Darkone83/Theia/images/2D Back Transmitter.png

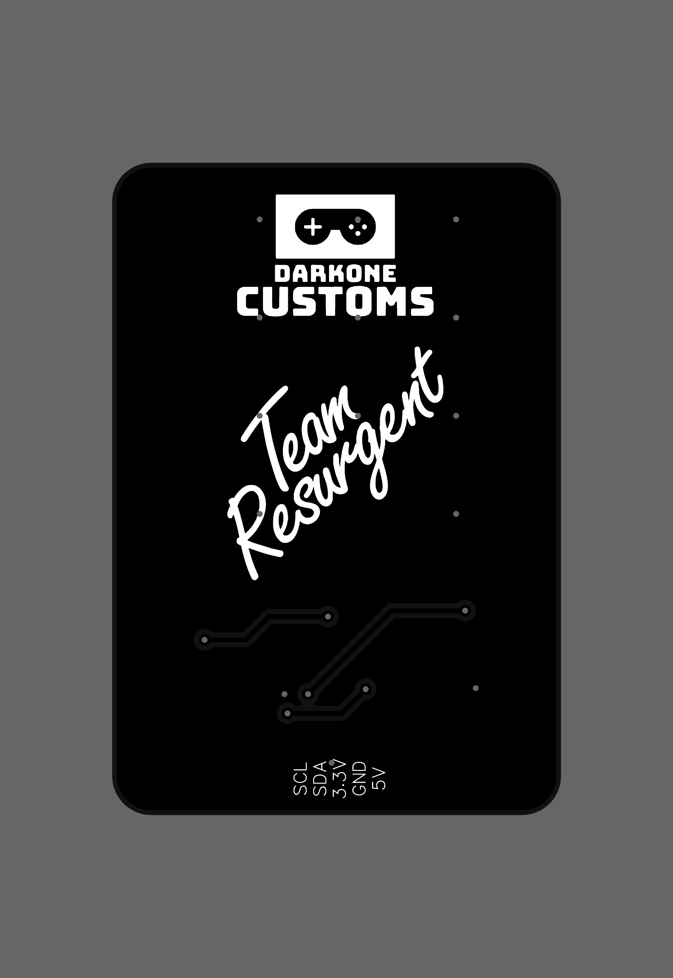
images/2D Back Transmitter.png
