Darkone83/Theia/images/3D Back Transmitter.png

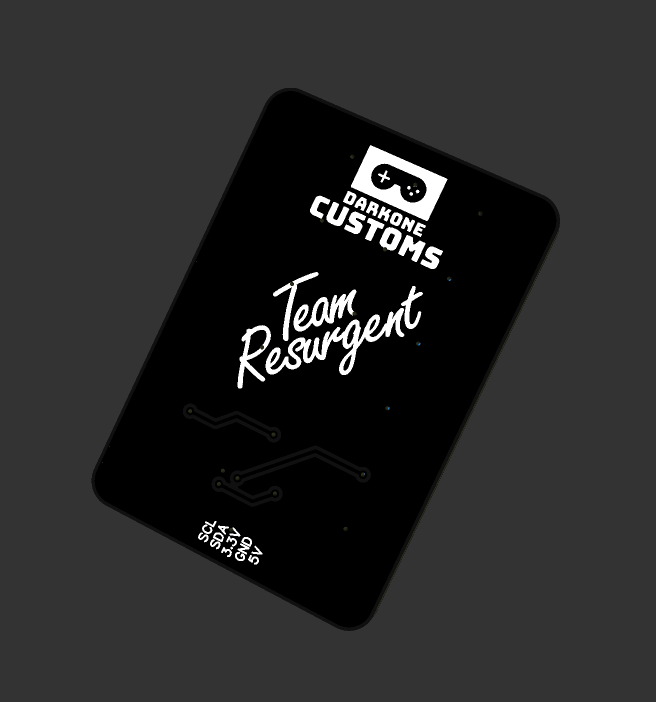
images/3D Back Transmitter.png
