Darkone83/Theia/images/3D Front US2066 Backpack.png

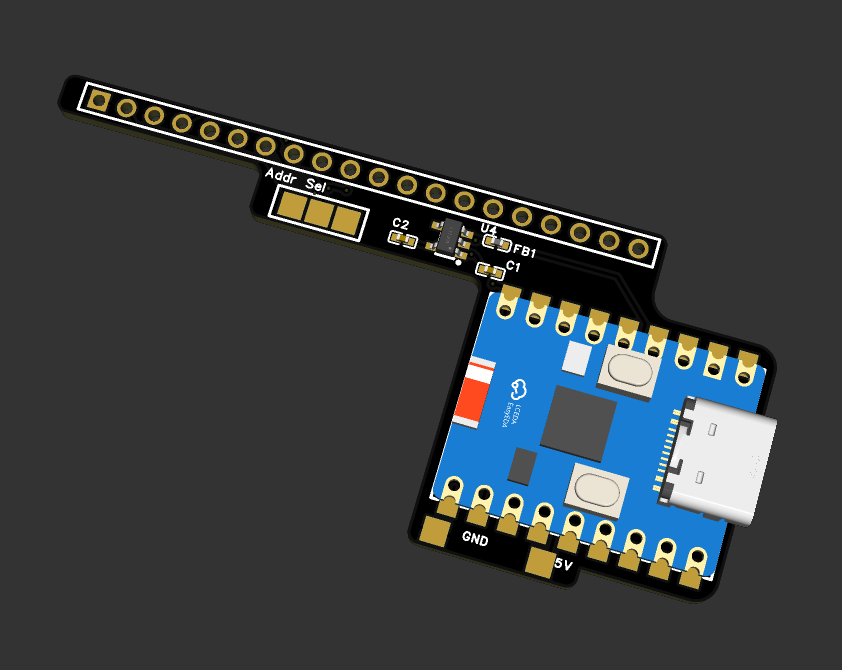
images/3D Front US2066 Backpack.png
